willherr72/OpenWatch/Code/watch code/watch project/src/lvgl_display.cpp

/**
 * @file lvgl_display.cpp
 * @brief LVGL display driver implementation for GC9A01A using Adafruit library
 */

#include "lvgl_display.h"
#include <SPI.h>

/* Static variables */
static Adafruit_GC9A01A *tft_ptr = nullptr;
static lv_disp_t *lvgl_display = nullptr;
static lv_disp_drv_t disp_drv;
static lv_disp_draw_buf_t draw_buf;

/* Draw buffer - 2 buffers for double buffering */
static lv_color_t draw_buf1[LVGL_BUFFER_SIZE];
static lv_color_t draw_buf2[LVGL_BUFFER_SIZE];

/**
 * @brief Flush callback for LVGL
 * Called when LVGL wants to update a region of the display
 */
static void lvgl_display_flush_cb(lv_disp_drv_t *disp, const lv_area_t *area, lv_color_t *color_p) {
    static int flush_count = 0;
    
    if (tft_ptr == nullptr) {
        Serial.println("[Display] ERROR: tft_ptr is null in flush callback!");
        lv_disp_flush_ready(disp);
        return;
    }

    uint32_t w = lv_area_get_width(area);
    uint32_t h = lv_area_get_height(area);

    if (flush_count < 5) {
        Serial.printf("[Display] Flush callback #%d: x1=%d, y1=%d, w=%d, h=%d\n", 
                      flush_count, area->x1, area->y1, w, h);
        flush_count++;
    }

    /* Start transaction */
    tft_ptr->startWrite();
    
    /* Set window and push pixels */
    tft_ptr->setAddrWindow(area->x1, area->y1, w, h);
    tft_ptr->writePixels((uint16_t *)color_p, w * h);
    
    /* End transaction */
    tft_ptr->endWrite();

    /* Tell LVGL we're done */
    lv_disp_flush_ready(disp);
}

/**
 * @brief Initialize LVGL display driver
 */
void lvgl_display_init(Adafruit_GC9A01A *tft) {
    tft_ptr = tft;

    /* Turn on backlight */
    #ifdef TFT_BL_PIN
        pinMode(TFT_BL_PIN, OUTPUT);
        digitalWrite(TFT_BL_PIN, HIGH);
        Serial.printf("[Display] Backlight enabled on GPIO %d\n", TFT_BL_PIN);
    #else
        Serial.println("[Display] WARNING: TFT_BL_PIN not defined!");
    #endif

    /* Initialize TFT */
    Serial.println("[Display] Calling tft->begin()...");
    Serial.flush();
    
    tft->begin();
    Serial.println("[Display] TFT begin() complete");
    Serial.flush();
    
    tft->setRotation(0);  // Portrait mode
    Serial.println("[Display] Rotation set");
    Serial.flush();
    
    /* Clear the display */
    Serial.println("[Display] Clearing screen...");
    Serial.flush();
    tft->fillScreen(0x0000);  // Black
    
    Serial.println("[Display] Display ready, initializing LVGL...");
    Serial.flush();

    /* Initialize LVGL */
    lv_init();
    Serial.println("[Display] LVGL lv_init() complete");
    Serial.flush();

    /* Initialize draw buffer */
    lv_disp_draw_buf_init(&draw_buf, draw_buf1, draw_buf2, LVGL_BUFFER_SIZE);
    Serial.println("[Display] LVGL draw buffer initialized");
    Serial.flush();
    
    /* Initialize display driver */
    lv_disp_drv_init(&disp_drv);
    disp_drv.hor_res = SCREEN_WIDTH;
    disp_drv.ver_res = SCREEN_HEIGHT;
    disp_drv.flush_cb = lvgl_display_flush_cb;
    disp_drv.draw_buf = &draw_buf;
    Serial.println("[Display] LVGL display driver configured");
    Serial.flush();
    
    /* Register display driver */
    lvgl_display = lv_disp_drv_register(&disp_drv);
    Serial.println("[Display] LVGL display driver registered");
    Serial.flush();

    Serial.println("[Display] LVGL display initialized");
    Serial.printf("[Display] Resolution: %dx%d\n", SCREEN_WIDTH, SCREEN_HEIGHT);
    Serial.printf("[Display] Buffer size: %d pixels per buffer\n", LVGL_BUFFER_SIZE);
}

/**
 * @brief Get LVGL display object
 */
lv_disp_t* lvgl_get_display() {
    return lvgl_display;
}
