willherr72/OpenWatch/Code/watch code/watch project/include/secrets.h

#pragma once
// Fill in your WiFi credentials. Do NOT commit real credentials to source control.
#define WIFI_SSID "HouseCats"
#define WIFI_PASS "Zoe-Will--1212!!"

// Weather data now uses weather.gov API (National Weather Service)
// No API key required - location is set to ZIP 77584 (Pearland, TX: 29.5636, -95.2861)
// To change location, edit the coordinates in weather_app.cpp fetchWeatherData()
